Yanisin/DotMatrix/src/BitbangIOTests/bitbang.c

/*
 * This file is part of the libopencm3 project.
 *
 * Copyright (C) 2009 Uwe Hermann <uwe@hermann-uwe.de>
 * Copyright (C) 2011 Stephen Caudle <scaudle@doceme.com>
 * Copyright (C) 2012 Karl Palsson <karlp@tweak.net.au>
 *
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
 * You should have received a copy of the GNU Lesser General Public License
 * along with this library.  If not, see <http://www.gnu.org/licenses/>.
 */

#include <libopencm3/stm32/rcc.h>
#include <libopencm3/stm32/gpio.h>
#include "hw_defs.h"

static void gpio_setup(void)
{
	/* Enable GPIOC clock. */
	/* Manually: */
	//RCC_AHBENR |= RCC_AHBENR_GPIOCEN;
	/* Using API functions: */
	rcc_periph_clock_enable(LED_RCC);
	rcc_periph_clock_enable(RCC_GPIOA);
	rcc_periph_clock_enable(RCC_GPIOB);


	/* Set GPIO8 (in GPIO port C) to 'output push-pull'. */
	/* Using API functions: */
	gpio_mode_setup(LED_PORT, GPIO_MODE_OUTPUT, GPIO_PUPD_NONE, LED_PIN);
	gpio_mode_setup(DISP_nOE_ROW_GPIO  , GPIO_MODE_OUTPUT, GPIO_PUPD_NONE,DISP_nOE_ROW_GPIO_PIN);
	gpio_mode_setup(DISP_nOE_COL_GPIO  , GPIO_MODE_OUTPUT, GPIO_PUPD_NONE,DISP_nOE_COL_GPIO_PIN  );
	gpio_mode_setup(DISP_COLS_CLK_GPIO  , GPIO_MODE_OUTPUT, GPIO_PUPD_NONE, DISP_COLS_CLK_GPIO_PIN  );
	gpio_mode_setup(DISP_COLS_DATA_GPIO  , GPIO_MODE_OUTPUT, GPIO_PUPD_NONE, DISP_COLS_DATA_GPIO_PIN  );
	gpio_mode_setup(DISP_COLS_STROBE_GPIO  , GPIO_MODE_OUTPUT, GPIO_PUPD_NONE, DISP_COLS_STROBE_GPIO_PIN  );
}

#define wait \
	for (i = 0; i < 500; i++) {	/* Wait a bit. */\
	__asm__("nop");\
	}\

static void bitbang(uint8_t col, uint8_t row)
{
	int k;
	gpio_clear(LED_PORT, LED_PIN);	/* LED on/off */

	for (k=0;k<8;k++) {
		if(col & (1<<k)) {
			gpio_set(DISP_COLS_DATA_GPIO, DISP_COLS_DATA_GPIO_PIN);
		} else {
			gpio_clear(DISP_COLS_DATA_GPIO, DISP_COLS_DATA_GPIO_PIN);
		}
		__asm__("nop");
		gpio_set(DISP_COLS_CLK_GPIO, DISP_COLS_CLK_GPIO_PIN);
		__asm__("nop");
		gpio_clear(DISP_COLS_CLK_GPIO, DISP_COLS_CLK_GPIO_PIN);
		__asm__("nop");
	}

	for (k=0;k<8;k++) {
		if(row & (1<<k)) {
			gpio_set(DISP_COLS_DATA_GPIO, DISP_COLS_DATA_GPIO_PIN);
		} else {
			gpio_clear(DISP_COLS_DATA_GPIO, DISP_COLS_DATA_GPIO_PIN);
		}
		__asm__("nop");
		gpio_set(DISP_COLS_CLK_GPIO, DISP_COLS_CLK_GPIO_PIN);
		__asm__("nop");
		gpio_clear(DISP_COLS_CLK_GPIO, DISP_COLS_CLK_GPIO_PIN);
		__asm__("nop");
	}

	/*strobe*/
	gpio_set(DISP_COLS_STROBE_GPIO, DISP_COLS_STROBE_GPIO_PIN);
	__asm__("nop");
	gpio_clear(DISP_COLS_STROBE_GPIO, DISP_COLS_STROBE_GPIO_PIN);
	__asm__("nop");
	
	gpio_set(LED_PORT, LED_PIN);	/* LED on/off */
	__asm__("nop");


}


int main(void)
{
	int i;
	int k = 0;

	gpio_setup();

	gpio_clear(DISP_nOE_ROW_GPIO, DISP_nOE_ROW_GPIO_PIN);
	gpio_clear(DISP_nOE_COL_GPIO, DISP_nOE_COL_GPIO_PIN);
	/* Blink the LED (PC8) on the board. */
	while (1) {
		/* Manually: */
		// GPIOC_BSRR = LED_PIN;		/* LED off */
		// for (i = 0; i < 1000000; i++)	/* Wait a bit. */
		//	__asm__("nop");
		// GPIOC_BRR = LED_PIN;			/* LED on */
		// for (i = 0; i < 1000000; i++)	/* Wait a bit. */
		//	__asm__("nop");

		/* Using API functions gpio_set()/gpio_clear(): */
		// gpio_set(LED_PORT, LED_PIN);		/* LED off */
		// for (i = 0; i < 1000000; i++)	/* Wait a bit. */
		//	__asm__("nop");
		// gpio_clear(LED_PORT, LED_PIN);	/* LED on */
		// for (i = 0; i < 1000000; i++)	/* Wait a bit. */
		//	__asm__("nop");

		/* Using API function gpio_toggle(): */
		bitbang(1 << k, 0xff & ~(1 << k));
		k = (k + 1) % 8;

		for (i = 0; i < 1000; i++)	/* Wait a bit. */
			__asm__("nop");

	}

	return 0;
}
