Yanisin/DotMatrix/src/full/hw/cdcacm.c

/*
 * This file is part of the libopencm3 project.
 *
 * Copyright (C) 2010 Gareth McMullin <gareth@blacksphere.co.nz>
 *
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
 * You should have received a copy of the GNU Lesser General Public License
 * along with this library.  If not, see <http://www.gnu.org/licenses/>.
 */

#include <stdlib.h>
#include <libopencm3/stm32/rcc.h>
#include <libopencm3/stm32/gpio.h>
#include <libopencm3/stm32/crs.h>
#include <libopencm3/usb/usbd.h>
#include <libopencm3/usb/cdc.h>
#include <libopencm3/cm3/nvic.h>
#include <hw/cdcacm.h>
#include <util/byte_queue.h>
#include <util/initializers.h>
#include <applets/applet.h>

#define RX_BUF_SIZE 64
#define TX_BUF_SIZE 64
#define USB_BUF_SIZE 32

static usbd_device *cdcacm_usbd_dev;
static int cdcacm_on;
static uint8_t cdcacm_tx_queue_buf[TX_BUF_SIZE];
output_queue_t cdcacm_tx_queue;
static bool cdcacm_tx_hw_empty = true;
/* Can be smaller, there is buffer in the shell */
static uint8_t cdcacm_rx_queue_buf[RX_BUF_SIZE];
input_queue_t cdcacm_rx_queue;

static const struct usb_device_descriptor dev = {
	.bLength = USB_DT_DEVICE_SIZE,
	.bDescriptorType = USB_DT_DEVICE,
	.bcdUSB = 0x0200,
	.bDeviceClass = USB_CLASS_CDC,
	.bDeviceSubClass = 0,
	.bDeviceProtocol = 0,
	.bMaxPacketSize0 = 64,
	.idVendor = 0x0483,
	.idProduct = 0x5740,
	.bcdDevice = 0x0200,
	.iManufacturer = 1,
	.iProduct = 2,
	.iSerialNumber = 3,
	.bNumConfigurations = 1,
};

/*
 * This notification endpoint isn't implemented. According to CDC spec its
 * optional, but its absence causes a NULL pointer dereference in Linux
 * cdc_acm driver.
 */
static const struct usb_endpoint_descriptor comm_endp[] = {{
	.bLength = USB_DT_ENDPOINT_SIZE,
	.bDescriptorType = USB_DT_ENDPOINT,
	.bEndpointAddress = 0x83,
	.bmAttributes = USB_ENDPOINT_ATTR_INTERRUPT,
	.wMaxPacketSize = 16,
	.bInterval = 255,
}};

static const struct usb_endpoint_descriptor data_endp[] = {{
	.bLength = USB_DT_ENDPOINT_SIZE,
	.bDescriptorType = USB_DT_ENDPOINT,
	.bEndpointAddress = 0x01,
	.bmAttributes = USB_ENDPOINT_ATTR_BULK,
	.wMaxPacketSize = 64,
	.bInterval = 1,
}, {
	.bLength = USB_DT_ENDPOINT_SIZE,
	.bDescriptorType = USB_DT_ENDPOINT,
	.bEndpointAddress = 0x82,
	.bmAttributes = USB_ENDPOINT_ATTR_BULK,
	.wMaxPacketSize = 64,
	.bInterval = 1,
}};

static const struct {
	struct usb_cdc_header_descriptor header;
	struct usb_cdc_call_management_descriptor call_mgmt;
	struct usb_cdc_acm_descriptor acm;
	struct usb_cdc_union_descriptor cdc_union;
} __attribute__((packed)) cdcacm_functional_descriptors = {
	.header = {
		.bFunctionLength = sizeof(struct usb_cdc_header_descriptor),
		.bDescriptorType = CS_INTERFACE,
		.bDescriptorSubtype = USB_CDC_TYPE_HEADER,
		.bcdCDC = 0x0110,
	},
	.call_mgmt = {
		.bFunctionLength =
			sizeof(struct usb_cdc_call_management_descriptor),
		.bDescriptorType = CS_INTERFACE,
		.bDescriptorSubtype = USB_CDC_TYPE_CALL_MANAGEMENT,
		.bmCapabilities = 0,
		.bDataInterface = 1,
	},
	.acm = {
		.bFunctionLength = sizeof(struct usb_cdc_acm_descriptor),
		.bDescriptorType = CS_INTERFACE,
		.bDescriptorSubtype = USB_CDC_TYPE_ACM,
		.bmCapabilities = 0,
	},
	.cdc_union = {
		.bFunctionLength = sizeof(struct usb_cdc_union_descriptor),
		.bDescriptorType = CS_INTERFACE,
		.bDescriptorSubtype = USB_CDC_TYPE_UNION,
		.bControlInterface = 0,
		.bSubordinateInterface0 = 1,
	 },
};

static const struct usb_interface_descriptor comm_iface[] = {{
	.bLength = USB_DT_INTERFACE_SIZE,
	.bDescriptorType = USB_DT_INTERFACE,
	.bInterfaceNumber = 0,
	.bAlternateSetting = 0,
	.bNumEndpoints = 1,
	.bInterfaceClass = USB_CLASS_CDC,
	.bInterfaceSubClass = USB_CDC_SUBCLASS_ACM,
	.bInterfaceProtocol = USB_CDC_PROTOCOL_AT,
	.iInterface = 0,

	.endpoint = comm_endp,

	.extra = &cdcacm_functional_descriptors,
	.extralen = sizeof(cdcacm_functional_descriptors),
}};

static const struct usb_interface_descriptor data_iface[] = {{
	.bLength = USB_DT_INTERFACE_SIZE,
	.bDescriptorType = USB_DT_INTERFACE,
	.bInterfaceNumber = 1,
	.bAlternateSetting = 0,
	.bNumEndpoints = 2,
	.bInterfaceClass = USB_CLASS_DATA,
	.bInterfaceSubClass = 0,
	.bInterfaceProtocol = 0,
	.iInterface = 0,

	.endpoint = data_endp,
}};

static const struct usb_interface ifaces[] = {{
	.num_altsetting = 1,
	.altsetting = comm_iface,
}, {
	.num_altsetting = 1,
	.altsetting = data_iface,
}};

static const struct usb_config_descriptor config = {
	.bLength = USB_DT_CONFIGURATION_SIZE,
	.bDescriptorType = USB_DT_CONFIGURATION,
	.wTotalLength = 0,
	.bNumInterfaces = 2,
	.bConfigurationValue = 1,
	.iConfiguration = 0,
	.bmAttributes = 0x80,
	.bMaxPower = 0x32,

	.interface = ifaces,
};

static const char *usb_strings[] = {
	"NoLeanThinking",
	"LED-Tile",
	"DEMO",
};

/* Buffer to be used for control requests. */
static uint8_t usbd_control_buffer[128];

static enum usbd_request_return_codes cdcacm_control_request(usbd_device *usbd_dev, struct usb_setup_data *req, uint8_t **buf,
		uint16_t *len, void (**complete)(usbd_device *usbd_dev, struct usb_setup_data *req))
{
	(void)complete;
	(void)buf;
	(void)usbd_dev;

	switch (req->bRequest) {
	case USB_CDC_REQ_SET_CONTROL_LINE_STATE: {
		/*
		 * This Linux cdc_acm driver requires this to be implemented
		 * even though it's optional in the CDC spec, and we don't
		 * advertise it in the ACM functional descriptor.
		 */
		char local_buf[10];
		struct usb_cdc_notification *notif = (void *)local_buf;

		/* We echo signals back to host as notification. */
		notif->bmRequestType = 0xA1;
		notif->bNotification = USB_CDC_NOTIFY_SERIAL_STATE;
		notif->wValue = 0;
		notif->wIndex = 0;
		notif->wLength = 2;
		local_buf[8] = req->wValue & 3;
		local_buf[9] = 0;
		// usbd_ep_write_packet(0x83, buf, 10);
		return USBD_REQ_HANDLED;
		}
	case USB_CDC_REQ_SET_LINE_CODING:
		if (*len < sizeof(struct usb_cdc_line_coding))
			return USBD_REQ_NOTSUPP;
		return USBD_REQ_HANDLED;
	}
	return USBD_REQ_NOTSUPP;
}

static void cdcacm_data_rx_cb(usbd_device *usbd_dev, uint8_t ep)
{
	uint16_t len;
	uint16_t count = 0;

	(void)ep;
	(void)usbd_dev;

	char buf[RX_BUF_SIZE];

	len = usbd_ep_read_packet(usbd_dev, 0x01, buf, 64);

	chSysLockFromISR();
	for (count = 0; count < len; count++)
		iqPutI(&cdcacm_rx_queue, buf[count]);
	chSysUnlockFromISR();
}

static void cdcacm_data_txI(usbd_device *usbd_dev, uint8_t ep)
{
	(void)ep;
	uint8_t buf[64];
	int len = 0;

	if (!cdcacm_on)
		return;

	while (!oqIsEmptyI(&cdcacm_tx_queue)) {
		buf[len++] = oqGetI(&cdcacm_tx_queue);
	}

	if (len) {
		usbd_ep_write_packet(usbd_dev, ep, (void*)buf, len);
	} else {
		cdcacm_tx_hw_empty = true;
	}
}

static void cdacm_data_tx_isr(usbd_device *usbd_dev, uint8_t ep)
{
	chSysLockFromISR();
	cdcacm_data_txI(usbd_dev, ep);
	chSysUnlockFromISR();
}

static void cdcacm_tx_queue_notify(output_queue_t *oq)
{
	(void)oq;
	/* Note: already S-locked */
	if (cdcacm_tx_hw_empty) {
		cdcacm_tx_hw_empty = false;
		cdcacm_data_txI(cdcacm_usbd_dev, 0x82);
	}
}

static void cdcacm_set_config(usbd_device *usbd_dev, uint16_t wValue)
{
	(void)wValue;
	(void)usbd_dev;

	usbd_ep_setup(usbd_dev, 0x01, USB_ENDPOINT_ATTR_BULK, 64, cdcacm_data_rx_cb);
	usbd_ep_setup(usbd_dev, 0x82, USB_ENDPOINT_ATTR_BULK, 64, cdacm_data_tx_isr);
	usbd_ep_setup(usbd_dev, 0x83, USB_ENDPOINT_ATTR_INTERRUPT, 16, NULL);

	usbd_register_control_callback(
				usbd_dev,
				USB_REQ_TYPE_CLASS | USB_REQ_TYPE_INTERFACE,
				USB_REQ_TYPE_TYPE | USB_REQ_TYPE_RECIPIENT,
				cdcacm_control_request);
	cdcacm_on = 1;
	cdacm_data_tx_isr(usbd_dev, 0x82);
}

/*
 * USB interrupt service
 */
void usb_isr(void)
{
	CH_IRQ_PROLOGUE();
	usbd_poll(cdcacm_usbd_dev);
	CH_IRQ_EPILOGUE();
}

/*
 * hardware specific USB setup
 */
static void usb_setup(void)
{
	rcc_periph_clock_enable(RCC_USB);
	crs_autotrim_usb_enable();
	rcc_set_usbclk_source(RCC_PLL);
}

int cdcacm_is_on(void)
{
	return cdcacm_on;
}

static void cdcacm_init(void)
{
	oqObjectInit(&cdcacm_tx_queue, cdcacm_tx_queue_buf, sizeof(cdcacm_tx_queue_buf),
		     cdcacm_tx_queue_notify, NULL);
	iqObjectInit(&cdcacm_rx_queue, cdcacm_rx_queue_buf, sizeof(cdcacm_rx_queue_buf), NULL, NULL);
	usb_setup();

	cdcacm_usbd_dev = usbd_init(&st_usbfs_v2_usb_driver, &dev, &config, usb_strings,
			3, usbd_control_buffer, sizeof(usbd_control_buffer));
	usbd_register_set_config_callback(cdcacm_usbd_dev, cdcacm_set_config);
	nvic_enable_irq(NVIC_USB_IRQ);
}
init_add(cdcacm_init);
