Yanisin/DotMatrix/src/full/applets/topo_applet.c

#include <hw/disp.h>
#include <util/icons.h>
#include <util/topo.h>
#include <applets/applet.h>

static void topo_applet_run(void)
{
	disp_set_rotation(topo_master_direction);
	disp_clean();

	if (topo_is_master) {
		draw_icon(icon_master, BLIT_SET);
	} else {
		draw_icon(icon_arrow, BLIT_SET);
	}

	bool checkerboard = (topo_master_position.x + topo_master_position.y) % 2;
	disp_set_rotation(topo_master_orientation);
	if (checkerboard) {
		draw_icon(icon_edge_line, BLIT_OR);
	} else {
		draw_icon(icon_top_edges, BLIT_OR);
	}

	applet_wait_for_end(TIME_INFINITE);
}

const struct applet topo_applet = {
	.run = topo_applet_run,
	.icon = {
		ICON_ROW(0, 1, 1, 0, 0, 0, 0, 0),
		ICON_ROW(0, 1, 1, 0, 0, 0, 0, 0),
		ICON_ROW(0, 0, 1, 0, 1, 1, 0, 0),
		ICON_ROW(0, 0, 1, 1, 1, 1, 0, 0),
		ICON_ROW(0, 0, 0, 1, 0, 1, 1, 1),
		ICON_ROW(0, 1, 1, 1, 0, 0, 1, 1),
		ICON_ROW(0, 1, 1, 0, 0, 0, 0, 0),
		ICON_ROW(0, 0, 0, 0, 0, 0, 0, 0),
	}
};


applet_add(topo);
