Yanisin/DotMatrix/src/full/chibi/chconf.h

#pragma once

#include "chconf_common.h"
#define _CHIBIOS_RT_CONF_
#define _CHIBIOS_RT_CONF_VER_6_0_

#define CH_CFG_ST_RESOLUTION                32
#define CH_CFG_ST_FREQUENCY                 1000
/* Periodic */
#define CH_CFG_ST_TIMEDELTA                 0

#define CH_CFG_INTERVALS_SIZE               32
#define CH_CFG_TIME_TYPES_SIZE              32
