Yanisin/DotMatrix/src/full/sim/sim.c

#define _GNU_SOURCE
#include <netdb.h>
#include <sys/types.h>
#include <sys/socket.h>
#include <stdlib.h>
#include <stdio.h>
#include <endian.h>
#include <arpa/inet.h>
#include <string.h>
#include <poll.h>
#include <hw/cell_id.h>
#include <hw/usart_buffered.h>
#include <hw/buttons.h>
#include <hw/i2c.h>
#include "sim.h"
#include "proto_defs.h"

#define MAX_MSG_SIZE 256

int server_socket;
uint8_t sim_recvbuf[MAX_MSG_SIZE];
bool sim_common_gpio = true;
bool sim_button_state[2];

static struct timespec next_tick;


struct msg_hdr {
	uint16_t len;
	uint16_t msgid;
};

bool sim_connect(const char *server, const char *port)
{
	struct addrinfo* ai;
	struct addrinfo hints;

	memset (&hints, 0, sizeof (hints));
	/* Python's soccketserver does not seem to support ipv6 yet */
	hints.ai_family = AF_INET;
	hints.ai_socktype = SOCK_STREAM;
	hints.ai_flags |= AI_CANONNAME;

	int r = getaddrinfo(server, port, &hints, &ai);
	if (r != 0) {
		fprintf(stderr, "can not resolve address: %s", gai_strerror(r));
		return false;
	}

	server_socket = socket(ai->ai_family, ai->ai_socktype, ai->ai_protocol);
	if (server_socket < 0) {
		perror("open socket");
		freeaddrinfo(ai);
		return false;
	}

	if (connect(server_socket, ai->ai_addr, ai->ai_addrlen) < 0) {
		fprintf(stderr, "Cannot connect to %s:%s\n", server, port);
		perror("connect");
		freeaddrinfo(ai);
		return false;
	}

	sim_send(MSGID_CLIENT_HELLO, CELL_ID_LEN, get_cell_id()->bytes);

	freeaddrinfo(ai);
	return true;
}


static void perror_fail(const char *msg)
{
	perror(msg);
	abort();
}

void sim_send(uint16_t msgid, uint16_t len, const void *data)
{
	ssize_t r;
	struct msg_hdr hdr = {
		.len = htobe16(len),
		.msgid = htobe16(msgid),
	};

	r = send(server_socket, &hdr, sizeof(hdr), 0);
	if (r != sizeof(hdr))
		perror_fail("send");

	r = send(server_socket, data, len, 0);
	if (r != len)
		perror_fail("send");
}

static void sim_recv(uint16_t *len, uint16_t *msgid)
{
	struct msg_hdr hdr;
	ssize_t r;
	r = recv(server_socket, &hdr, sizeof(hdr), MSG_WAITALL);
	if (r != sizeof(hdr))
		perror_fail("recv");
	*len = be16toh(hdr.len);
	*msgid = be16toh(hdr.msgid);
	if (*len > MAX_MSG_SIZE) {
		fprintf(stderr, "oversize message received from server, len = 0x%x\n", *len);
		abort();
	}
	r = recv(server_socket, sim_recvbuf, *len, MSG_WAITALL);
	if (r != *len)
		perror_fail("recv");
}

static void sim_dispatch(uint16_t len, uint16_t msgid)
{
	switch (msgid) {
	case MSGID_GPIO_INPUT_STATE:
		sim_common_gpio = sim_recvbuf[0];
		break;
	case MSGID_UART_RX:
		usart_sim_recv(sim_recvbuf[0], sim_recvbuf + 1, len -1);
		break;
	case MSGID_BUTTON_UP:
		button_isr(sim_recvbuf[0], false);
		break;
	case MSGID_BUTTON_DOWN:
		button_isr(sim_recvbuf[0], true);
		break;
	case MSGID_I2C_RX:
		i2c_sim_recv(len, sim_recvbuf);
		break;
	}
}

#define NS (1000*1000*1000)
static void advance_tick(void)
{
	next_tick.tv_nsec += NS/CH_CFG_ST_FREQUENCY;
	while (next_tick.tv_nsec >= NS) {
		next_tick.tv_nsec -= NS;
		next_tick.tv_sec += 1;
	}
}

static bool is_before(const struct timespec *a, const struct timespec *b)
{
	return (a->tv_sec < b->tv_sec) ||
		((a->tv_sec == b->tv_sec) && (a->tv_nsec < b->tv_nsec));
}

void sim_irq_wait(bool wait) {
	struct timespec now;
	struct pollfd pfd;
	int rv;
	struct timespec tout;
	uint16_t len, msgid;

	if (next_tick.tv_sec == 0) {
		clock_gettime(CLOCK_MONOTONIC, &next_tick);
		advance_tick();
	}
	clock_gettime(CLOCK_MONOTONIC, &now);
	if (is_before(&next_tick, &now)) {
		chSysLockFromISR();
		chSysTimerHandlerI();
		chSysUnlockFromISR();
		advance_tick();
	}


	if (wait) {
		tout = next_tick;
		clock_gettime(CLOCK_MONOTONIC, &now);
		if (tout.tv_nsec < now.tv_nsec) {
			tout.tv_nsec += 1000*1000*1000;
			tout.tv_sec--;
		}
		if (tout.tv_sec < now.tv_sec) {
			return;
		}
		tout.tv_sec -= now.tv_sec;
		tout.tv_nsec -= now.tv_nsec;
	} else {
		tout.tv_sec = 0;
		tout.tv_nsec = 0;
	}


	pfd.fd = server_socket;
	pfd.events = POLLIN;
	rv = ppoll(&pfd, 1, &tout, NULL);
	if (rv == 0)
		return;
	if (rv < 0) {
		perror("poll");
		abort();
	}

	sim_recv(&len, &msgid);
	sim_dispatch(len, msgid);
}
